sparkfun/SparkFun_Ultrasonic_Distance_Sensor-Qwiic/docs/assets/img/24805_SparkFun_Ultrasonic_Distance_Sensor-Receive.jpg

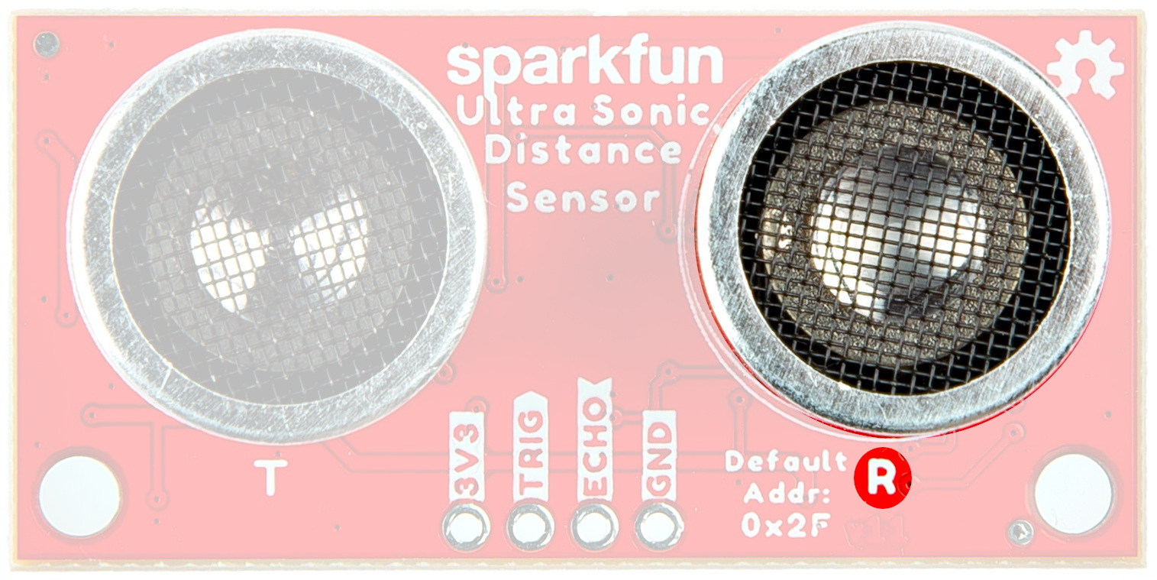
docs/assets/img/24805_SparkFun_Ultrasonic_Distance_Sensor-Receive.jpg
