sparkfun/SparkFun_Ultrasonic_Distance_Sensor-Qwiic/Firmware/stm8l15x_it.c

/**
******************************************************************************
* @file    Project/STM8L15x_StdPeriph_Template/stm8l15x_it.c
* @author  MCD Applicatin Team
* @version V1.5.0
* @date    13-May-2011
* @brief   Main Interrupt Service Routines.
*          This file provides template for all peripherals interrupt service
*routine.
******************************************************************************
* @attention
*
* THE PRESENT FIRMWARE WHICH IS FOR GUIDANCE ONLY AIMS AT PROVIDING CUSTOMERS
* WITH CODING INFORMATION REGARDING THEIR PRODUCTS IN ORDER FOR THEM TO SAVE
* TIME. AS A RESULT, STMICROELECTRONICS SHALL NOT BE HELD LIABLE FOR ANY
* DIRECT, INDIRECT OR CONSEQUENTIAL DAMAGES WITH RESPECT TO ANY CLAIMS ARISING
* FROM THE CONTENT OF SUCH FIRMWARE AND/OR THE USE MADE BY CUSTOMERS OF THE
* CODING INFORMATION CONTAINED HEREIN IN CONNECTION WITH THEIR PRODUCTS.
*
* <h2><center>&copy; COPYRIGHT 2011 STMicroelectronics</center></h2>
******************************************************************************
*/

/* Includes ------------------------------------------------------------------*/
#include "STM8L15x_StdPeriph_Driver/inc/stm8l15x_gpio.h"
#include "main.h"

// Following variables are used for I2C communication.
uint16_t event = 0x00;
volatile uint8_t rxIndex = 0;
volatile uint8_t txIndex = 0;
extern uint8_t userAddress;
extern volatile uint8_t peripheralBuffer[kBufferSize];

// Following variables are used for interrupt flags and are used by both this file and main.c.
extern volatile uint8_t outRangeFlag;
extern volatile uint8_t opAmpInterrupt;
extern volatile uint8_t addressInterrupt;
extern volatile uint8_t triggerInterrupt;
extern volatile uint8_t i2cInterrupt;

// Following variables are used for distance calculations and are used by both this file and main.c.
extern volatile uint8_t distanceH, distanceL;

#ifdef _COSMIC_
/**
 * @brief Dummy interrupt routine
 * @par Parameters:
 * None
 * @retval
 * None
 */
INTERRUPT_HANDLER(NonHandledInterrupt, 0)
{
}
#endif

INTERRUPT_HANDLER_TRAP(TRAP_IRQHandler)
{
    /* In order to detect unexpected events during development,
       it is recommended to set a breakpoint on the following instruction.
    */
}
/**
 * @brief FLASH Interrupt routine.
 * @param  None
 * @retval None
 */
INTERRUPT_HANDLER(FLASH_IRQHandler, 1)
{
    /* In order to detect unexpected events during development,
       it is recommended to set a breakpoint on the following instruction.
    */
}

/**
 * @brief External IT PIN3 Interrupt routine, on the trigger pin.
 * @param  None
 * @retval None
 */
INTERRUPT_HANDLER(EXTI3_IRQHandler, 11)
{
    EXTI_ClearITPendingBit(EXTI_IT_Pin3);
    triggerInterrupt = 1;
}

/*
 * @brief External IT PIN5 Interrupt routine, on the address pin.
 * @param  None
 * @retval None
 */

@svlreg INTERRUPT_HANDLER(EXTI5_IRQHandler, 13)
{
    EXTI_ClearITPendingBit(EXTI_IT_Pin5);
    addressInterrupt = 1;
}

/**
 * @brief Main Interrupt Pin triggered by the ultrasonic sensor.
 * @param  None
 * @retval None
 */
INTERRUPT_HANDLER(EXTI6_IRQHandler, 14)
{
    EXTI_ClearITPendingBit(EXTI_IT_Pin6);
    setOpAmp(kDisableOpAmp);
    opAmpInterrupt = 1;
}

/**
 * @brief TIM2 Update/Overflow/Trigger/Break/USART2 TX Interrupt routine, tracks the number 
 * of cycles between when a pulse is sent out by the transmitter and then received. Aids in 
 * calculating the distance.
 * @param  None
 * @retval None
 */
INTERRUPT_HANDLER(TIM2_UPD_OVF_TRG_BRK_USART2_TX_IRQHandler, 19)
{
    TIM2_ClearITPendingBit(TIM2_IT_Update);
    setOpAmp(kDisableOpAmp);
    TIM2_Cmd(DISABLE);
    outRangeFlag = 1;
}

/**
 * @brief Timer3 Update/Overflow/Trigger/Break Interrupt routine, used for trigger pin timeout.
 * @param  None
 * @retval None
 */
INTERRUPT_HANDLER(TIM3_UPD_OVF_TRG_BRK_USART3_TX_IRQHandler, 21)
{
    TIM3_ClearITPendingBit(TIM3_IT_Update);
    setOpAmp(kDisableOpAmp);
    GPIO_ResetBits(GPIOB, GPIO_Pin_2);
    TIM3_Cmd(DISABLE);
    outRangeFlag = 1;
    triggerInterrupt = 0;
}

/**
 * @brief TIM4 Update/Overflow/Trigger Interrupt routine, used for floating the inverting pin on the op-amp.
 * @param  None
 * @retval None
 */
@svlreg INTERRUPT_HANDLER(TIM4_UPD_OVF_TRG_IRQHandler, 25)
{
    TIM4_ClearITPendingBit(TIM4_IT_Update);
    GPIO_Init(GPIOB, (GPIO_Pin_TypeDef)GPIO_Pin_4, GPIO_Mode_In_FL_No_IT); // PB4
    TIM4_Cmd(DISABLE);
}

/**
 * @brief Interrupt routine for I2C and SPI2 events
 * @param  None
 * @retval None
 */
@svlreg INTERRUPT_HANDLER(I2C1_SPI2_IRQHandler, 29)
{

    if (I2C_ReadRegister(I2C1, I2C_Register_SR2))
    {
        // Clears SR2 register
        I2C1->SR2 = 0;
        distanceH = 0;
        distanceL = 0;
    }

    event = I2C_GetLastEvent(I2C1);
    switch (event)
    {
        /* check on EV1 */
    case I2C_EVENT_SLAVE_TRANSMITTER_ADDRESS_MATCHED:
        txIndex = 0;
        break;
        /* check on EV3 */
    case I2C_EVENT_SLAVE_BYTE_TRANSMITTING:
        I2C_SendData(I2C1, distanceH);
        I2C_SendData(I2C1, distanceL);
        break;
        /* check on EV1*/
    case I2C_EVENT_SLAVE_RECEIVER_ADDRESS_MATCHED:
        rxIndex = 0;
        break;
        /* Check on EV2*/
    case I2C_EVENT_SLAVE_BYTE_RECEIVED:
        i2cInterrupt = 0;
        peripheralBuffer[rxIndex++] = I2C_ReceiveData(I2C1);
        break;
    case (I2C_EVENT_SLAVE_STOP_DETECTED):
        /* write to CR2 to clear STOPF flag */
        I2C1->CR2 |= I2C_CR2_ACK;
        rxIndex = 0;
        i2cInterrupt = 1;
        break;

    default:
        break;
    }
}

/******************* (C) COPYRIGHT 2011 STMicroelectronics *****END OF
   FILE****/
