sparkfun/SparkFun_Ultrasonic_Distance_Sensor-Qwiic/Firmware/stm8l15x_it.h

/**
  ******************************************************************************
  * @file    Project/STM8L15x_StdPeriph_Template/stm8l15x_it.h
  * @author  MCD Application Team
  * @version V1.5.0
  * @date    13-May-2011
  * @brief   This file contains the headers of the interrupt handlers.
  ******************************************************************************
  * @attention
  *
  * THE PRESENT FIRMWARE WHICH IS FOR GUIDANCE ONLY AIMS AT PROVIDING CUSTOMERS
  * WITH CODING INFORMATION REGARDING THEIR PRODUCTS IN ORDER FOR THEM TO SAVE
  * TIME. AS A RESULT, STMICROELECTRONICS SHALL NOT BE HELD LIABLE FOR ANY
  * DIRECT, INDIRECT OR CONSEQUENTIAL DAMAGES WITH RESPECT TO ANY CLAIMS ARISING
  * FROM THE CONTENT OF SUCH FIRMWARE AND/OR THE USE MADE BY CUSTOMERS OF THE
  * CODING INFORMATION CONTAINED HEREIN IN CONNECTION WITH THEIR PRODUCTS.
  *
  * <h2><center>&copy; COPYRIGHT 2011 STMicroelectronics</center></h2>
  ******************************************************************************
  */ 

/* Define to prevent recursive inclusion -------------------------------------*/
#ifndef __STM8L15x_IT_H
#define __STM8L15x_IT_H

/* Includes ------------------------------------------------------------------*/
#include "stm8l15x.h"

/* Exported types ------------------------------------------------------------*/
/* Exported constants --------------------------------------------------------*/
/* Exported macro ------------------------------------------------------------*/
/* Exported functions ------------------------------------------------------- */
#ifdef _COSMIC_
 void _stext(void); /* RESET startup routine */
 INTERRUPT void NonHandledInterrupt(void);
#endif /* _COSMIC_ */

#ifndef _RAISONANCE_
 INTERRUPT void TRAP_IRQHandler(void); /* TRAP */
 INTERRUPT void FLASH_IRQHandler(void); /* FLASH EOP/PG_DIS */
 INTERRUPT void DMA1_CHANNEL0_1_IRQHandler(void); /* DMA1 Channel0/1*/
 INTERRUPT void DMA1_CHANNEL2_3_IRQHandler(void); /*DMA1 Channel2/3*/
 INTERRUPT void RTC_CSSLSE_IRQHandler(void); /* RTC /CSS_LSE */
 INTERRUPT void EXTIE_F_PVD_IRQHandler(void); /*EXTI PORTE/EXTI PORTF/PVD*/
 INTERRUPT void EXTIB_G_IRQHandler(void); /* EXTI PORTB / EXTI PORTG */
 INTERRUPT void EXTID_H_IRQHandler(void); /* EXTI PORTD / EXTI PORTH*/
 INTERRUPT void EXTI0_IRQHandler(void); /* EXTI PIN0 */
 INTERRUPT void EXTI1_IRQHandler(void); /* EXTI PIN1 */
 INTERRUPT void EXTI2_IRQHandler(void); /* EXTI PIN2 */
 INTERRUPT void EXTI3_IRQHandler(void); /* EXTI PIN3 */
 INTERRUPT void EXTI4_IRQHandler(void); /* EXTI PIN4 */
 INTERRUPT void EXTI5_IRQHandler(void); /* EXTI PIN5 */
 INTERRUPT void EXTI6_IRQHandler(void); /* EXTI PIN6 */
 INTERRUPT void EXTI7_IRQHandler(void); /* EXTI PIN7 */
 INTERRUPT void LCD_AES_IRQHandler(void); /* LCD /AES */
 INTERRUPT void SWITCH_CSS_BREAK_DAC_IRQHandler(void); /* Switch CLK/CSS/TIM1 Break/DAC */
 INTERRUPT void ADC1_COMP_IRQHandler(void); /*ADC1/COMP*/
 INTERRUPT void TIM2_UPD_OVF_TRG_BRK_USART2_TX_IRQHandler(void); /* TIM2 UPD/OVF/TRG/BRK / USART2 TX */
 INTERRUPT void TIM2_CC_USART2_RX_IRQHandler(void); /* TIM2 CAP / USART2 RX */
 INTERRUPT void TIM3_UPD_OVF_TRG_BRK_USART3_TX_IRQHandler(void); /* TIM3 UPD/OVF/TRG/BRK /USART3 TX*/
 INTERRUPT void TIM3_CC_USART3_RX_IRQHandler(void); /* TIM3 CAP/ USART3 RX */
 INTERRUPT void TIM1_UPD_OVF_TRG_COM_IRQHandler(void);/* TIM1 UPD/OVF/TRG/COM */
 INTERRUPT void TIM1_CC_IRQHandler(void);/* TIM1 CAP*/
 INTERRUPT void TIM4_UPD_OVF_TRG_IRQHandler(void); /* TIM4 UPD/OVF/TRI */
 INTERRUPT void SPI1_IRQHandler(void); /* SPI1 */
 INTERRUPT void USART1_TX_TIM5_UPD_OVF_TRG_BRK_IRQHandler(void); /* USART1 TX / TIM5 UPD/OVF/TRG/BRK */
 INTERRUPT void USART1_RX_TIM5_CC_IRQHandler(void); /* USART1 RX / TIM5 CAP */
 INTERRUPT void I2C1_SPI2_IRQHandler(void); /* I2C1 / SPI2 */
#endif /* _RAISONANCE_ */


#endif /* __STM8L15x_IT_H */

/******************* (C) COPYRIGHT 2011 STMicroelectronics *****END OF FILE****/
